jambuur/APEDSK99/Arduino/libraries-ADD TO YOUR IDE/arduino-FTP-master/FTP.cpp

/*
   Copyright (c) 2019 Boot&Work Corp., S.L. All rights reserved

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
   You should have received a copy of the GNU Lesser General Public License
   along with this library.  If not, see <http://www.gnu.org/licenses/>.
 */

#include "FTP.h"

#define BUFF_SIZE 64

static char buff[BUFF_SIZE];
static size_t buffLen = 0;

////////////////////////////////////////////////////////////////////////////////////////////////////
FTP::FTP(Client &cClient, Client &dClient) : cClient(cClient), dClient(dClient) {
}

////////////////////////////////////////////////////////////////////////////////////////////////////
int FTP::connect(IPAddress ip, uint16_t port, const char *user, const char *password) {
	return connect(ip, port) && auth(user, password);
}

////////////////////////////////////////////////////////////////////////////////////////////////////
int FTP::connect(const char *host, uint16_t port, const char *user, const char *password) {
	return connect(host, port) && auth(user, password);
}

////////////////////////////////////////////////////////////////////////////////////////////////////
int FTP::connect(IPAddress ip, uint16_t port) {
	return cClient.connect(ip, port) && cClient.connected();
}

////////////////////////////////////////////////////////////////////////////////////////////////////
int FTP::connect(const char *host, uint16_t port) {
	return cClient.connect(host, port) && cClient.connected();
}

////////////////////////////////////////////////////////////////////////////////////////////////////
int FTP::auth(const char *user, const char *password) {
	if (!user) {
		return 0;
	}

	if (waitServerCode() != 220) {
		return 0;
	}

	switch (waitServerCode(F("USER"), user)) {
		case 331:
			if (!password) {
				return 0;
			}

			if (waitServerCode(F("PASS"), password) != 230) {
				return 0;
			}
			break;

		case 230:
			// Logged in
			break;

		default:
			return 0;
	}

	return 1;
}

////////////////////////////////////////////////////////////////////////////////////////////////////
int FTP::beginTransaction() {
	if (!cClient.connected()) {
		return 0;
	}

	if (!waitServerCode(F("TYPE I"), nullptr, 200)) {
		return 0;
	}

	cClient.println(F("PASV"));
#if DEBUG
	Serial.print("> ");
	Serial.println(F("PASV"));
#endif

	char pasvResponse[70];
	if (waitServerCode(pasvResponse) != 227) {
		return 0;
	}

	uint8_t params[6];
	char *ptr = strtok(pasvResponse, "(");
	for (int i = 0; i < 6; ++i) {
		ptr = strtok(nullptr, ",");
		if (!ptr) {
			return 0;
		}
		params[i] = atoi(ptr);
	}

	IPAddress dataAddress(params[0], params[1], params[2], params[3]);
	uint16_t dataPort = (uint16_t(params[4]) << 8) | (params[5] & 0xff);

	dClient.connect(dataAddress, dataPort);
	if (!dClient.connected()) {
		return 0;
	}

	return 1;
}

////////////////////////////////////////////////////////////////////////////////////////////////////
size_t FTP::retrieve(const char *fileName, Stream &stream) {
	if (!beginTransaction()) {
		return 0;
	}

	bool alreadyClosed = false;
	int code = waitServerCode(F("RETR"), fileName);
	switch (code) {
		case 125: // Data connection already open
		case 150: // Data connection opened
			break;
		case 226: // Data connection already closed
			alreadyClosed = true;
			break;
		default:
			quit();
			return 0;
	}

	uint32_t startTime = millis();
	uint8_t chunk[_FTP_CHUNK_SIZE];
	size_t size = 0;
	do {
		size_t len = dClient.available();
		if (len > 0) {
			if (len > _FTP_CHUNK_SIZE) {
				len = _FTP_CHUNK_SIZE;
			}

			startTime = millis();
			len = dClient.read(chunk, len);
			if (stream.write(chunk, len) == 0) {
				break;
			}
			size += len;
		} else if (!dClient.connected()) {
			break;
		} else {
			delay(1);
		}
	} while (millis() - startTime < _FTP_TIMEOUT);

	dClient.stop();

	if (alreadyClosed) {
		if (waitServerCode() != 226) {
			return 0;
		}
	}

	return size;
}

////////////////////////////////////////////////////////////////////////////////////////////////////
size_t FTP::store(const char *fileName, Stream &stream) {
	if (!beginTransaction()) {
		return 0;
	}

	int code = waitServerCode(F("STOR"), fileName);
	switch (code) {
		case 125: // Data connection already open
		case 150: // Data connection opened
			break;
		default:
			return 0;
	}

	uint8_t chunk[_FTP_CHUNK_SIZE];
	size_t size = 0;
	do {
		size_t len = stream.available();
		if (len == 0) {
			break;
		}
		if (len > _FTP_CHUNK_SIZE) {
			len = _FTP_CHUNK_SIZE;
		}
		len = stream.readBytes(chunk, len);
		if (dClient.write(chunk, len) == 0) {
			break;
		}
		size += len;
	} while (true);

	dClient.stop();

	if (waitServerCode() != 226) {
		return 0;
	}

	return size;
}

////////////////////////////////////////////////////////////////////////////////////////////////////
int FTP::waitServerCode(const __FlashStringHelper *cmd, const char *arg, uint16_t response) {
	return waitServerCode(cmd, arg, nullptr) == response;
}

////////////////////////////////////////////////////////////////////////////////////////////////////
uint16_t FTP::waitServerCode(const __FlashStringHelper *cmd, const char *arg, char *desc) {
	cClient.print(cmd);
#if DEBUG
	Serial.print("> ");
	Serial.print(cmd);
#endif

	if (arg) {
		cClient.print(' ');
		cClient.print(arg);
#if DEBUG
		Serial.print(' ');
		Serial.print(arg);
#endif
	}

	cClient.println();
#if DEBUG
	Serial.println();
#endif

	return waitServerCode(desc);
}

////////////////////////////////////////////////////////////////////////////////////////////////////
uint16_t FTP::waitServerCode(char *desc) {
	uint32_t startTime = millis();
	size_t len;
	do {
		len = cClient.available();
		delay(1);
	} while ((len < 4) && (millis() - startTime <= _FTP_TIMEOUT));

	if (len == 0) {
		return 0;
	}

#if DEBUG
	Serial.print("< ");
#endif

	uint16_t code = 0;
	bool codeDone = false;
	bool descDone = false;
	do {
		len = cClient.available();
		if (len > 0) {
			if (len + buffLen > BUFF_SIZE) {
				len = BUFF_SIZE - buffLen;
			}
			buffLen += cClient.read(buff + buffLen, len);

			char *ptr = buff;
			char c;
			while (buffLen > 0) {
				c = *ptr++;
				--buffLen;

				if (c == '\r') {
#if DEBUG
					Serial.print("<CR>");
#endif
					// Nothing to do
				} else if (c == '\n') {
#if DEBUG
					Serial.println("<NL>");
#endif
					descDone = true;
					break;
				} else {
#if DEBUG
					Serial.print(c);
#endif
					if (!codeDone) {
						if (c == ' ') {
							codeDone = true;
						} else {
							code *= 10;
							code += c - '0';
						}
					} else if (desc) {
						*desc++ = c;
					}
				}
			}

			if (buffLen == BUFF_SIZE) {
				buffLen = 0;
			} else if (buffLen > 0) {
				memcpy(buff, ptr, buffLen);
			}
		}
	} while ((millis() - startTime <= _FTP_TIMEOUT) && !descDone);

	if (desc) {
		*desc = '\0';
	}

	return code;
}

////////////////////////////////////////////////////////////////////////////////////////////////////
void FTP::stop() {
	if (cClient.connected()) {
		quit();
		cClient.stop();
	}
}

////////////////////////////////////////////////////////////////////////////////////////////////////
void FTP::quit() {
	waitServerCode(F("QUIT"));
	if (dClient.connected()) {
		dClient.stop();
	}
}
